DavidMolTor/PhonoPreamp/PowerSupply/Design/PowerSupply_Front.png

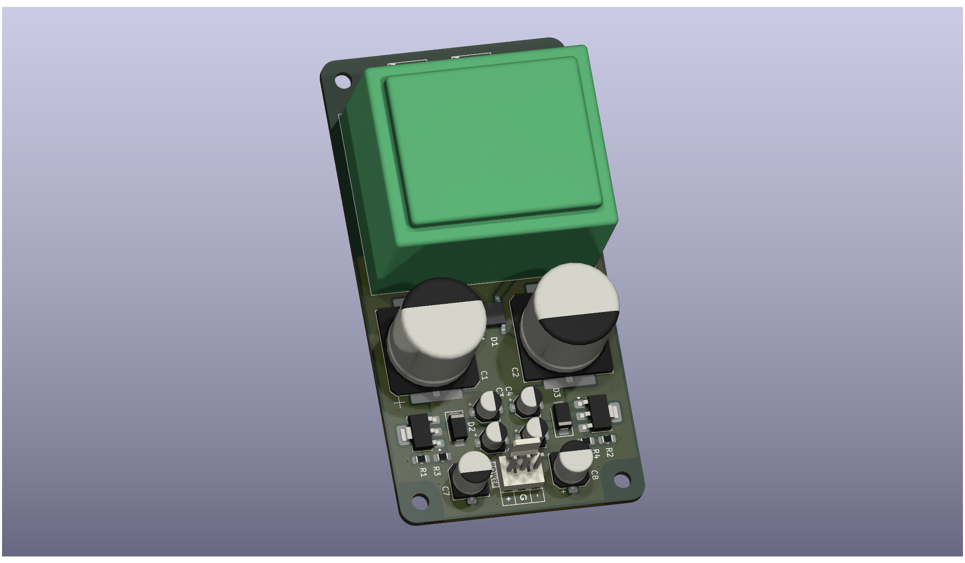
PowerSupply/Design/PowerSupply_Front.png
